hboyce4/Atmel_MPPT/Simulation/Sim Hacheur/Captures/temps stabilisation inter-step.PNG

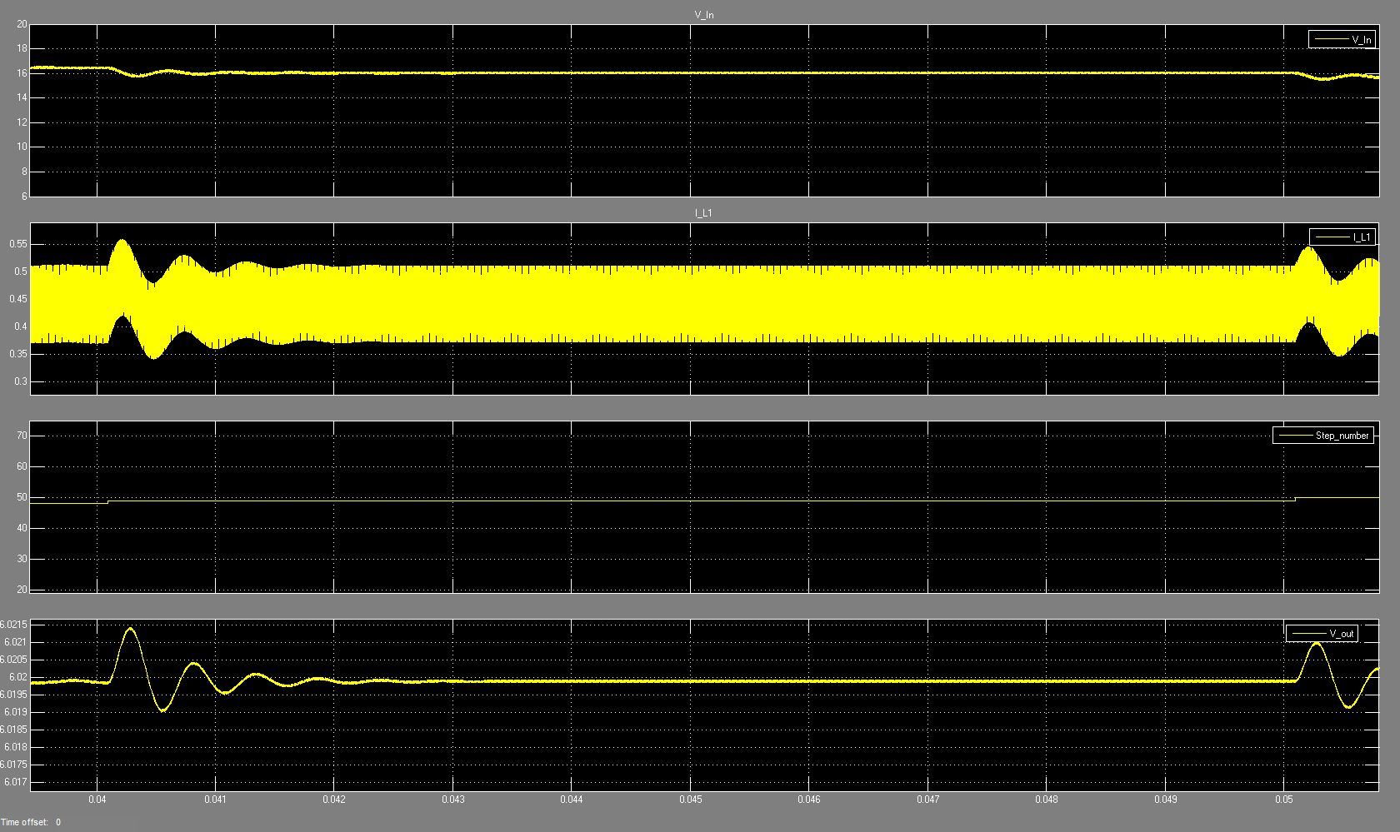
Simulation/Sim Hacheur/Captures/temps stabilisation inter-step.PNG
